Quiklearner2099/The_Signet/PCB/PCB Back.png

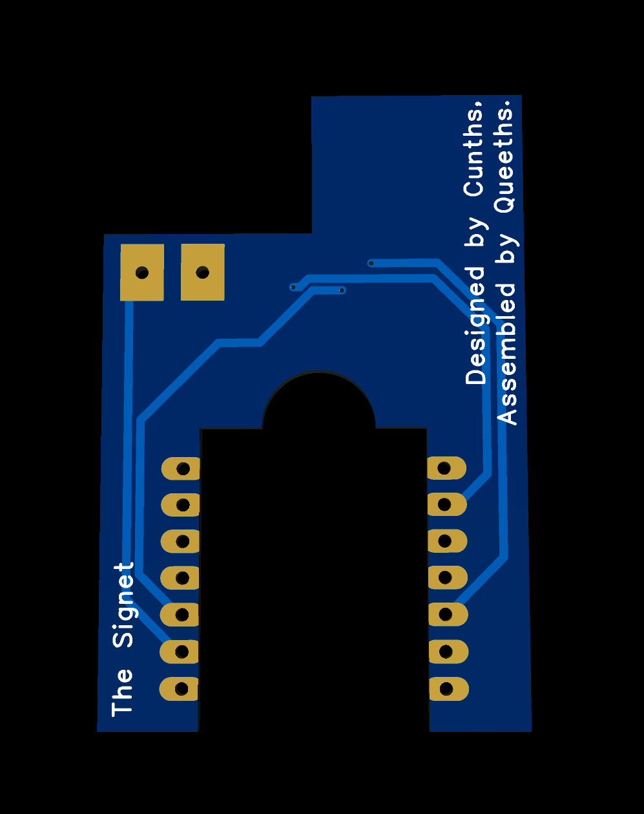
PCB/PCB Back.png
