Quiklearner2099/The_Signet/PCB/PCB Front.png

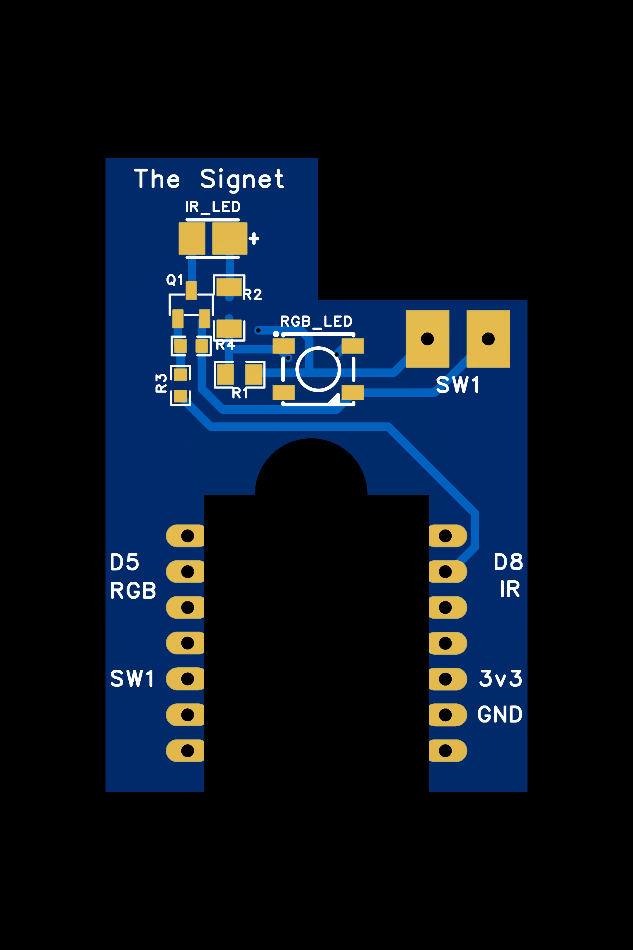
PCB/PCB Front.png
