Quiklearner2099/The_Signet/Pictures/Exploded View.jpg

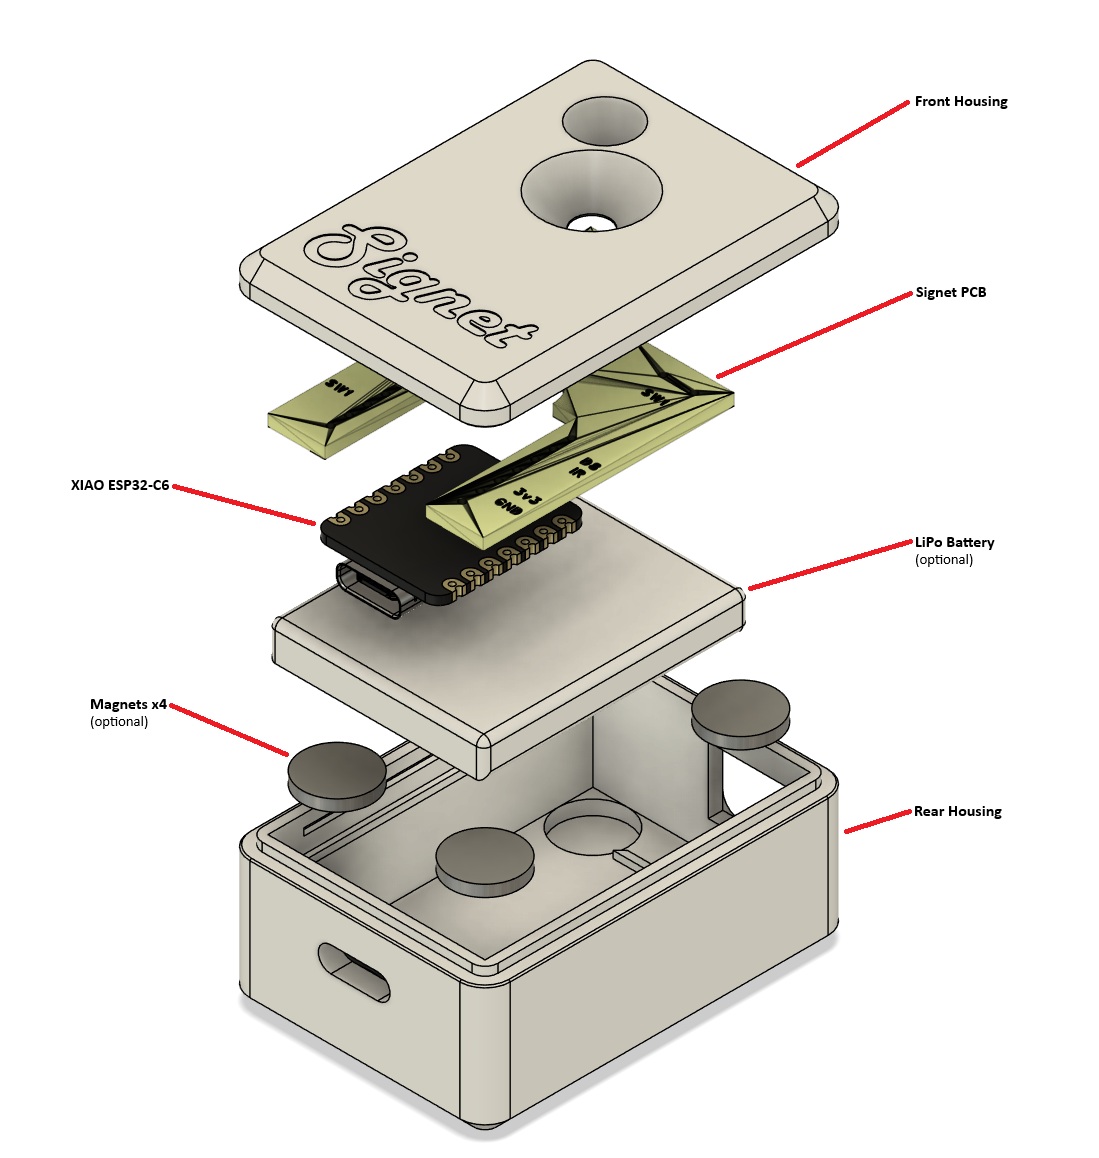
Pictures/Exploded View.jpg
