Quiklearner2099/The_Signet/Pictures/Help 1.jpg

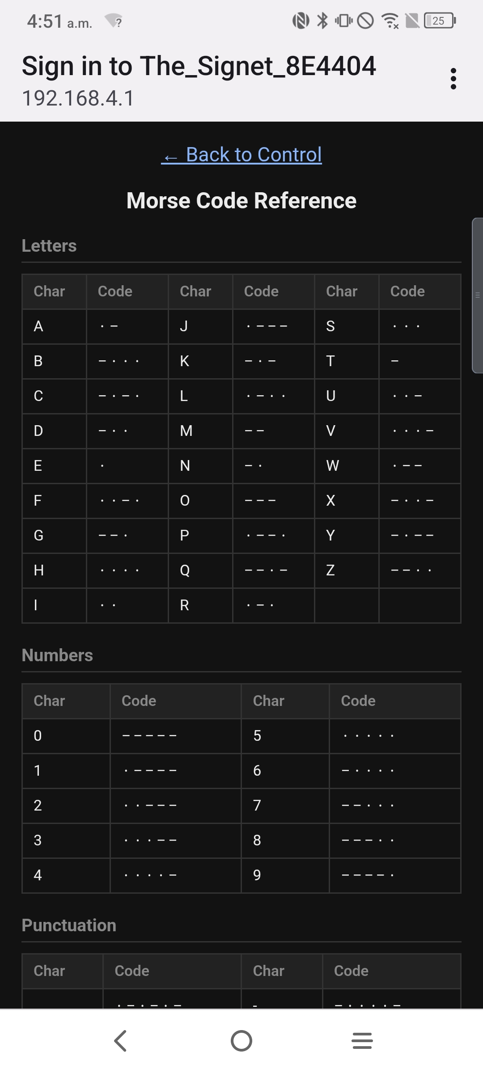
Pictures/Help 1.jpg
