Quiklearner2099/The_Signet/Pictures/Help 2.jpg

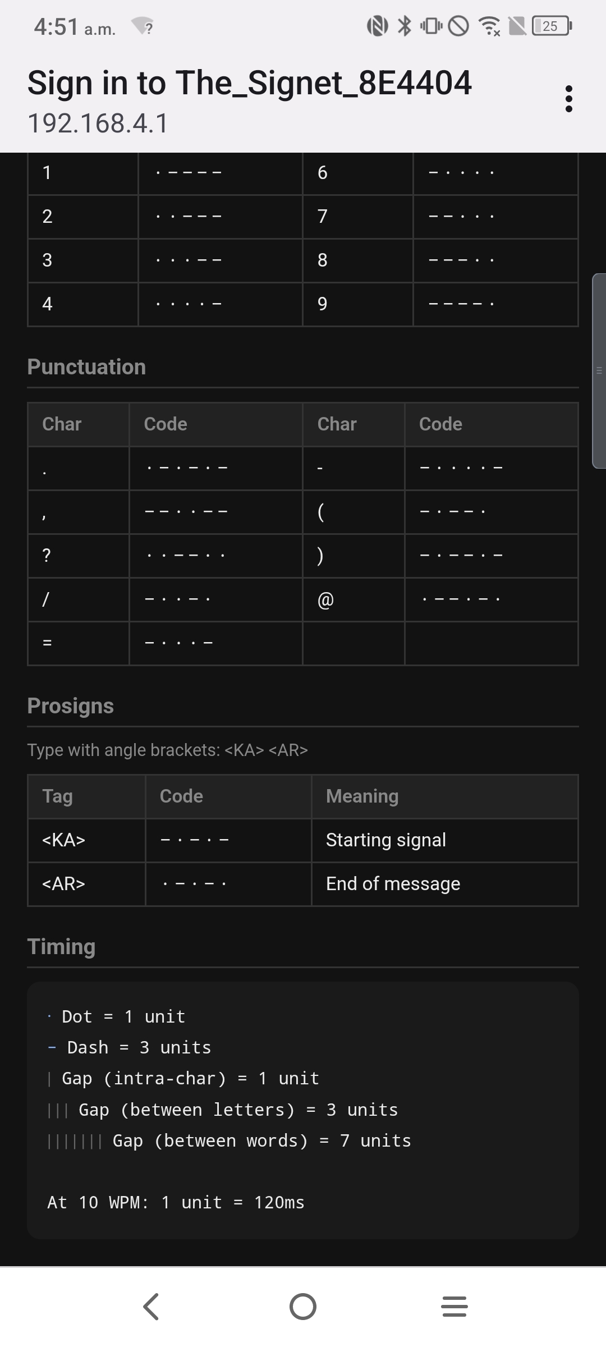
Pictures/Help 2.jpg
