Quiklearner2099/The_Signet/Pictures/ITU_Morse_Code_Chart.jpg

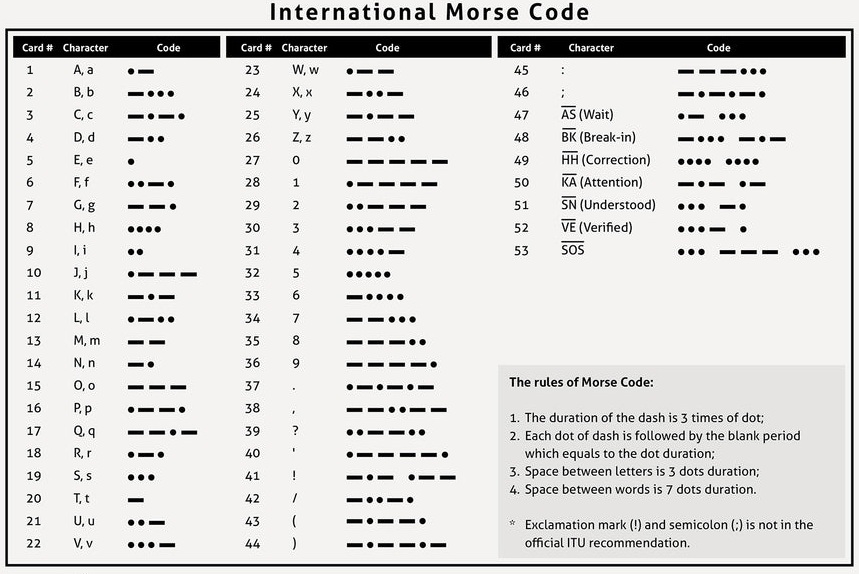
Pictures/ITU_Morse_Code_Chart.jpg
