Quiklearner2099/The_Signet/Pictures/Settings.jpg

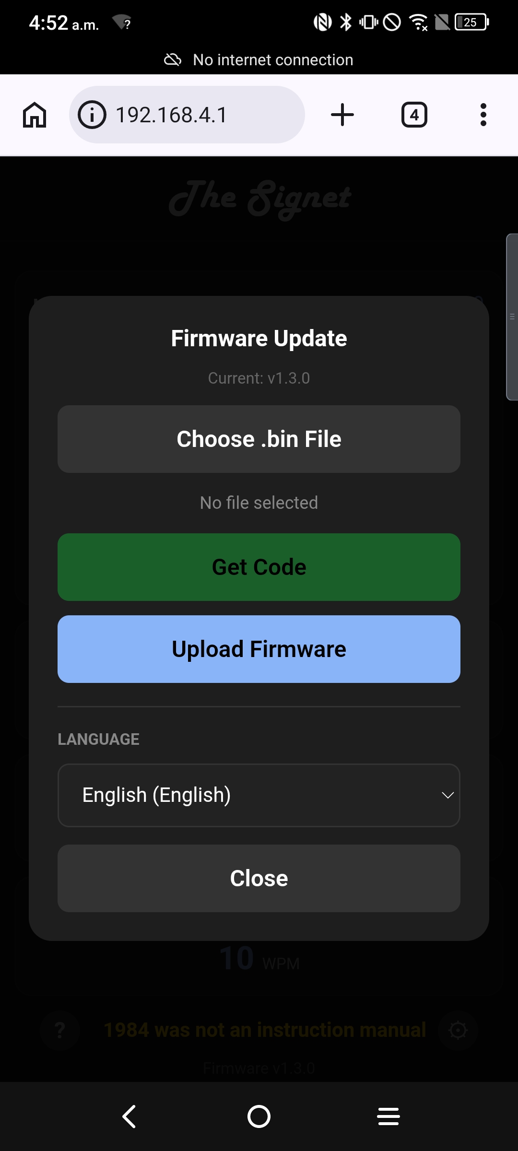
Pictures/Settings.jpg
