Quiklearner2099/The_Signet/Pictures/Signet 3.JPG

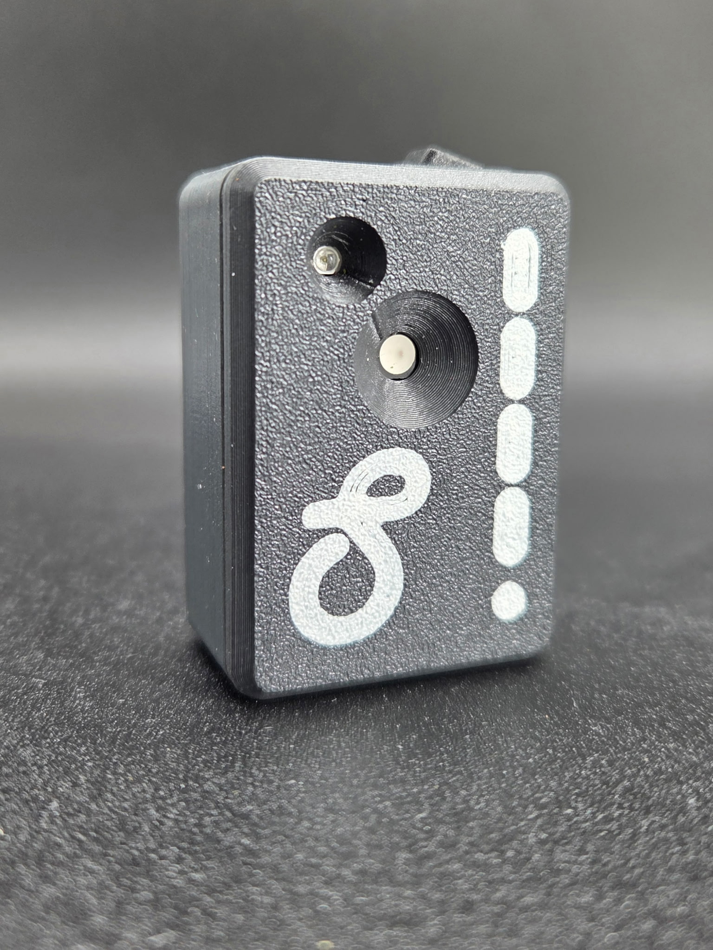
Pictures/Signet 3.JPG
