Quiklearner2099/The_Signet/Pictures/Signet 4.JPG

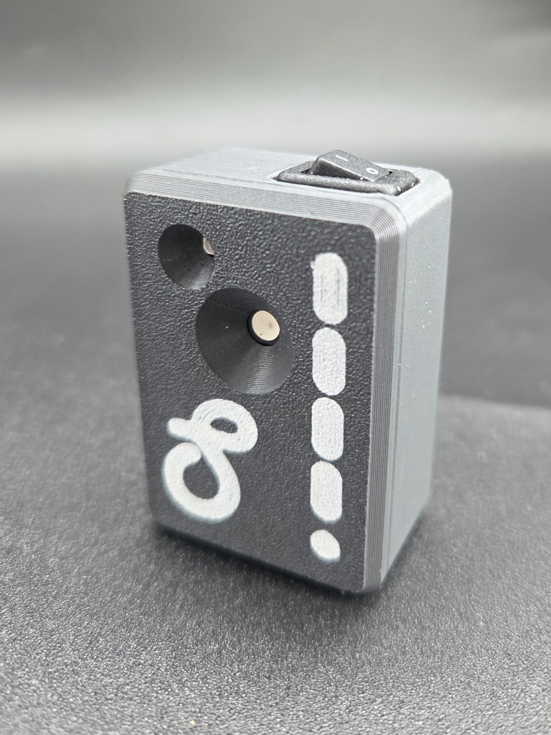
Pictures/Signet 4.JPG
