Quiklearner2099/The_Signet/Pictures/Signet 6.JPG

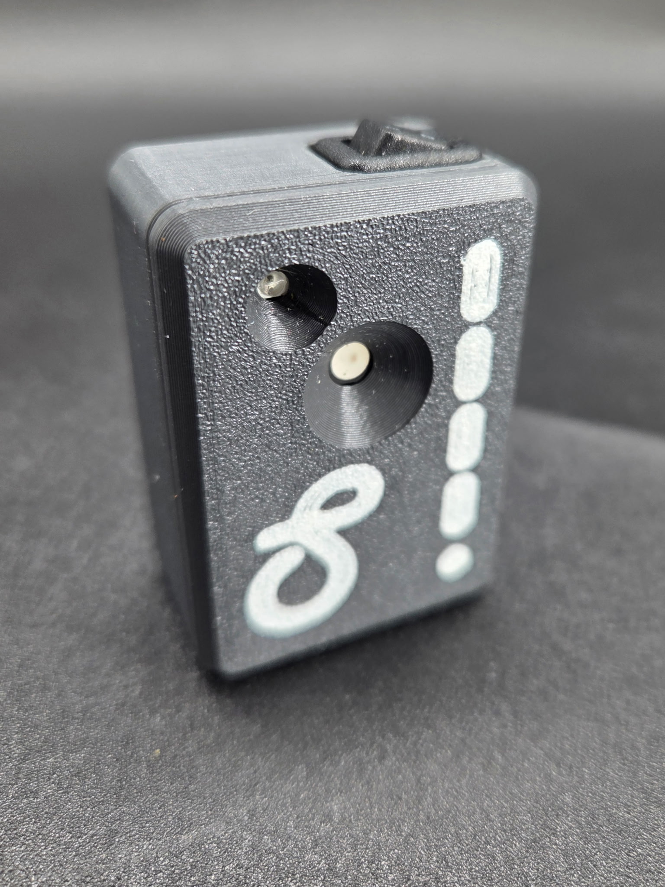
Pictures/Signet 6.JPG
