Quiklearner2099/The_Signet/Pictures/Signet 7.JPG

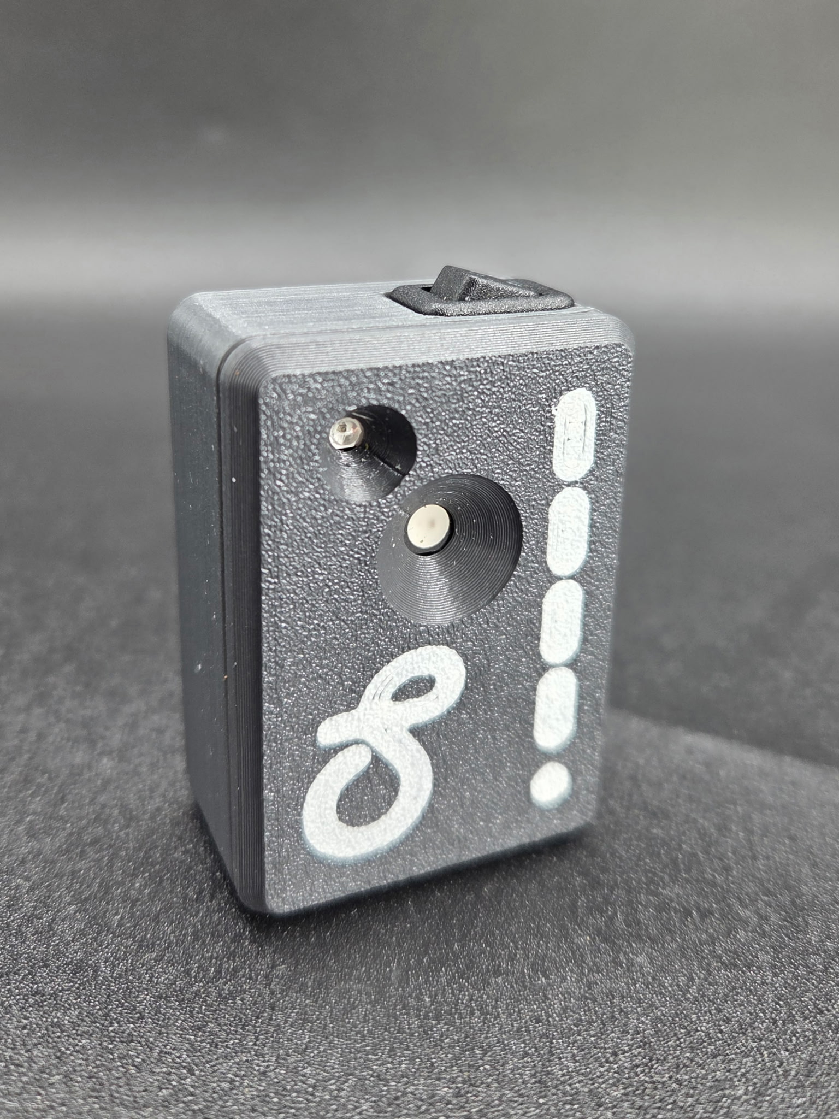
Pictures/Signet 7.JPG
