Quiklearner2099/The_Signet/Pictures/Signet 8.JPG

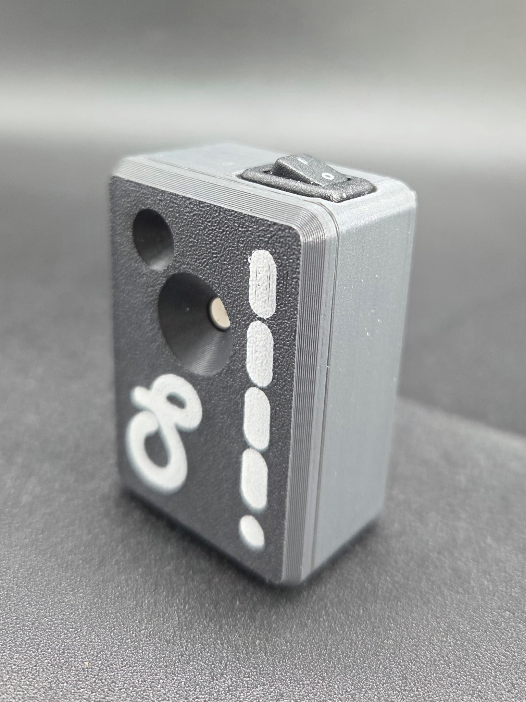
Pictures/Signet 8.JPG
