Quiklearner2099/The_Signet/Pictures/Signet 9.JPG

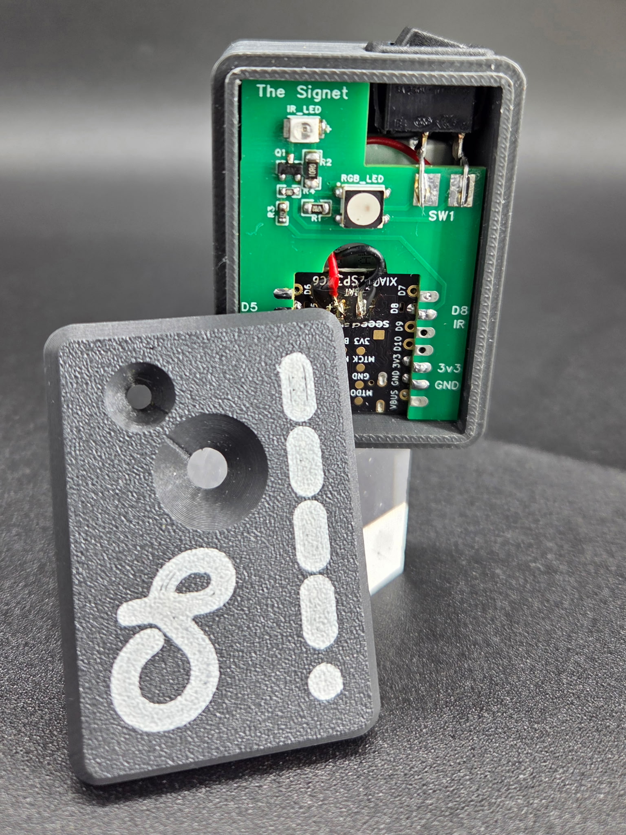
Pictures/Signet 9.JPG
