Quiklearner2099/The_Signet/Pictures/Switch.jpg

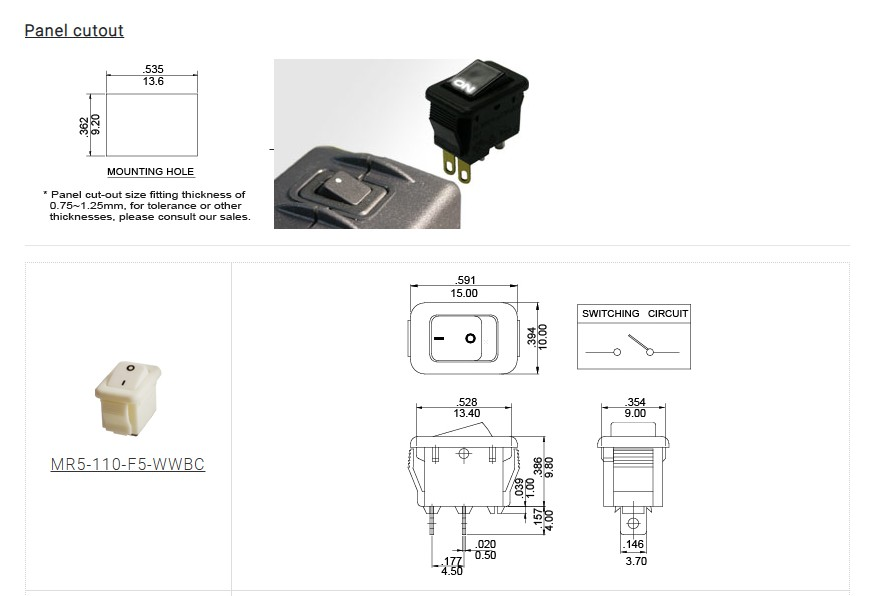
Pictures/Switch.jpg
